jvegaf/mixduino/docs/midi/mixduino_dist.png

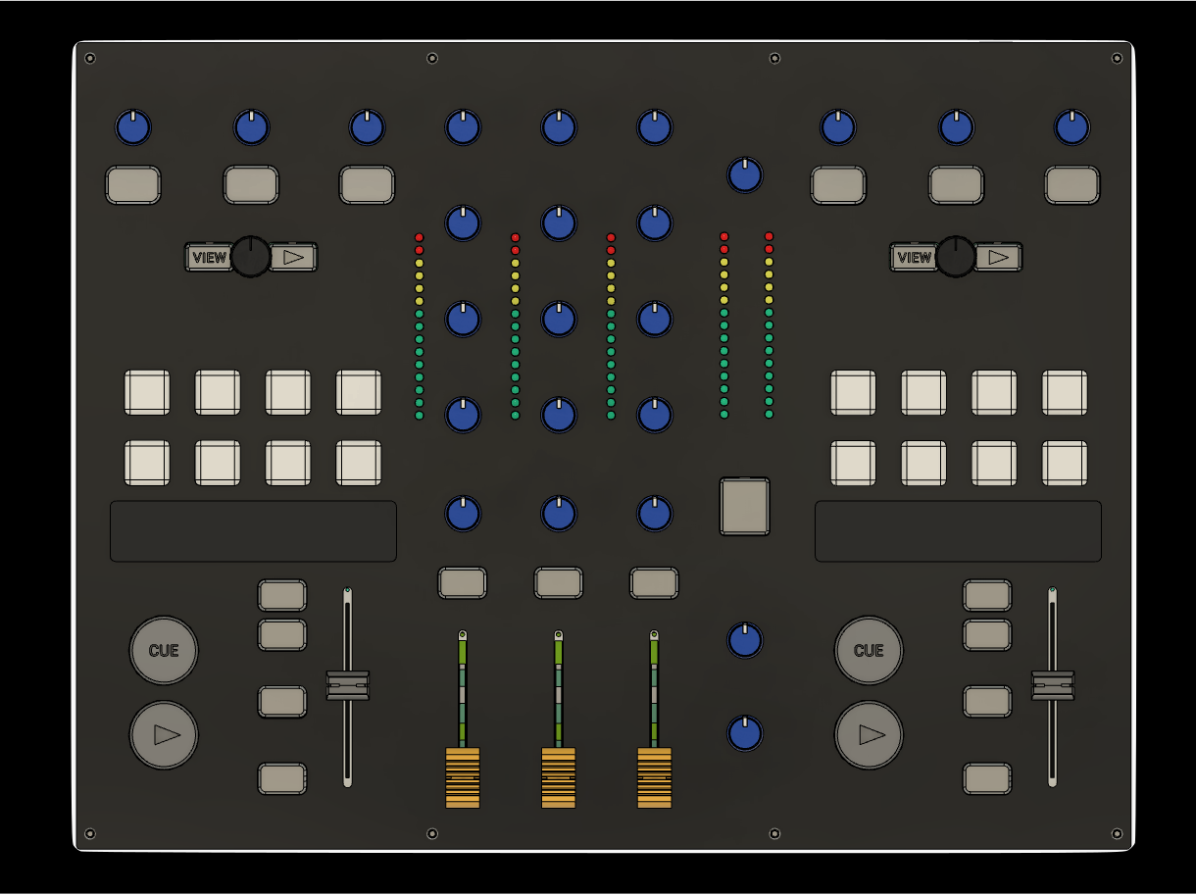
docs/midi/mixduino_dist.png
