jvegaf/mixduino/docs/pads/pads-dim1.png

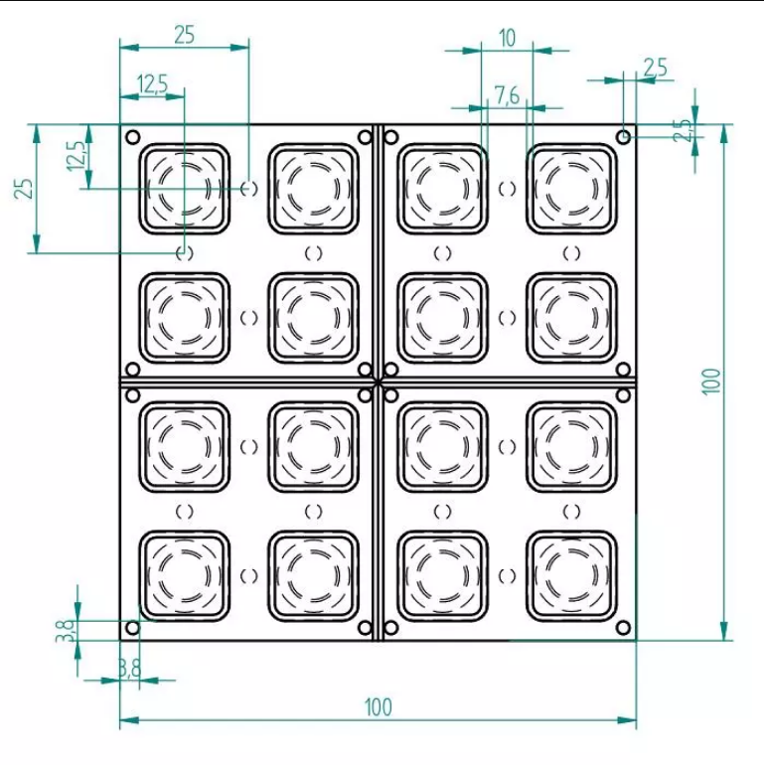
docs/pads/pads-dim1.png
