jvegaf/mixduino/docs/pads/pads-dim2.png

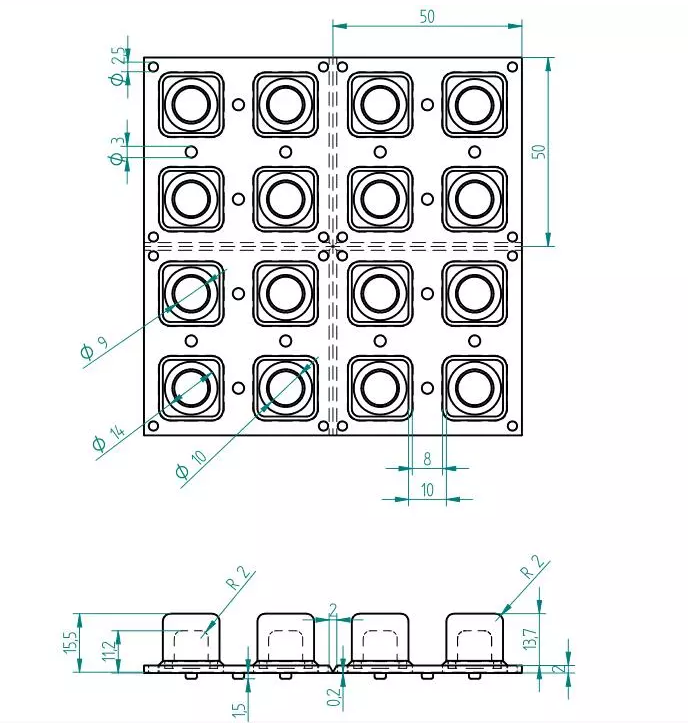
docs/pads/pads-dim2.png
