jvegaf/mixduino/PCB/Kicad/3d-models/WS2812B.step

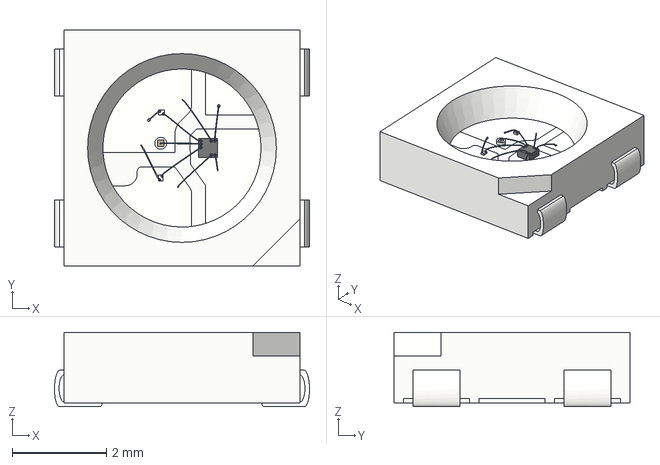
[picture p25: CAD file, 2021-04-04]
PCB/Kicad/3d-models/WS2812B.step
5.40 x 5.00 x 1.57 mm
