jvegaf/mixduino/PCB/Kicad/3d-models/Resistor_SMD_0,25W_1206.stp

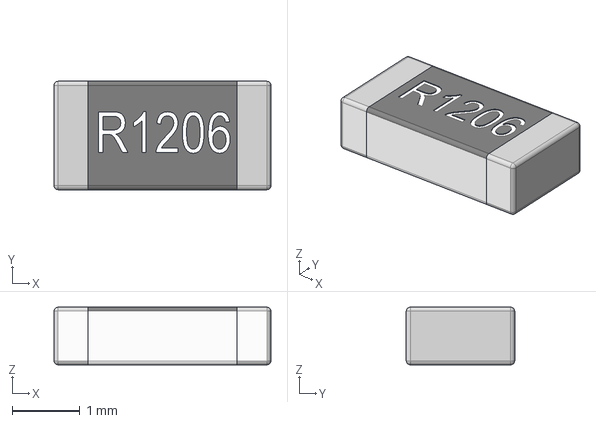
[picture p26: CAD file, 2021-04-04]
PCB/Kicad/3d-models/Resistor_SMD_0,25W_1206.stp
3.20 x 1.60 x 0.85 mm
