jvegaf/mixduino/PCB/Kicad/3d-models/LED D3 - Yellow_cutted.step

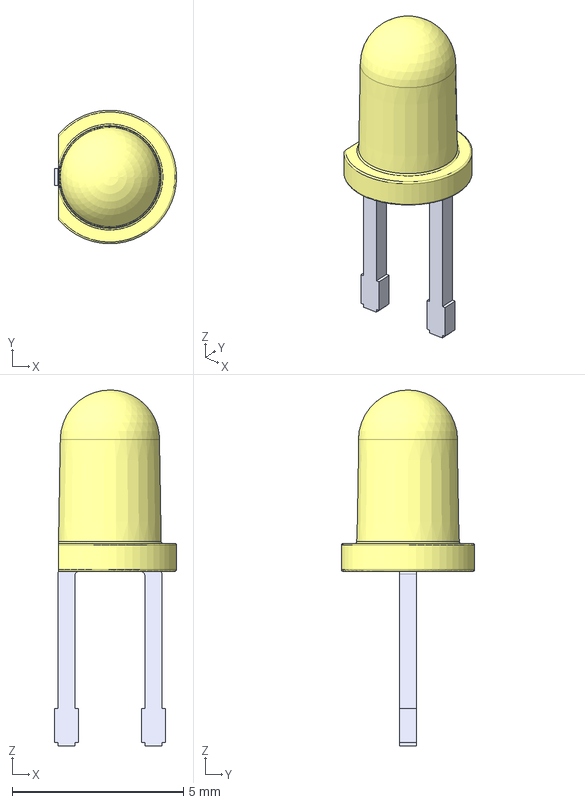
[picture p27: CAD file, 2021-04-04]
PCB/Kicad/3d-models/LED D3 - Yellow_cutted.step
3.57 x 3.90 x 10.4 mm
