jvegaf/mixduino/PCB/Kicad/3d-models/SW3dPS-SOIC24.STEP

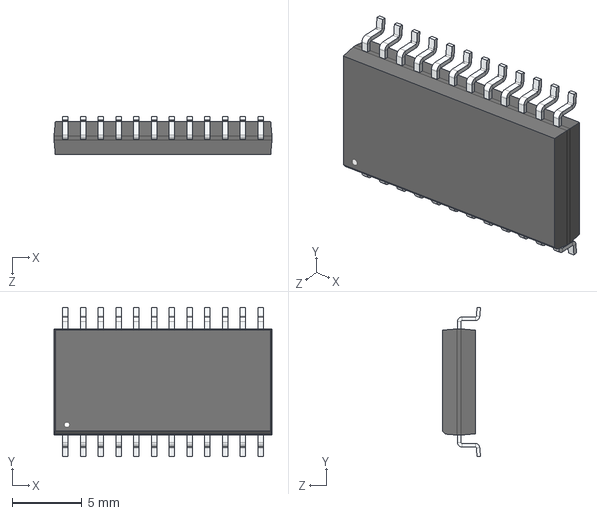
[picture p28: CAD file, 2021-04-04]
PCB/Kicad/3d-models/SW3dPS-SOIC24.STEP
15.6 x 10.7 x 2.72 mm
