jvegaf/mixduino/PCB/Kicad/3d-models/75mm Straight Slide Potentiometer.step

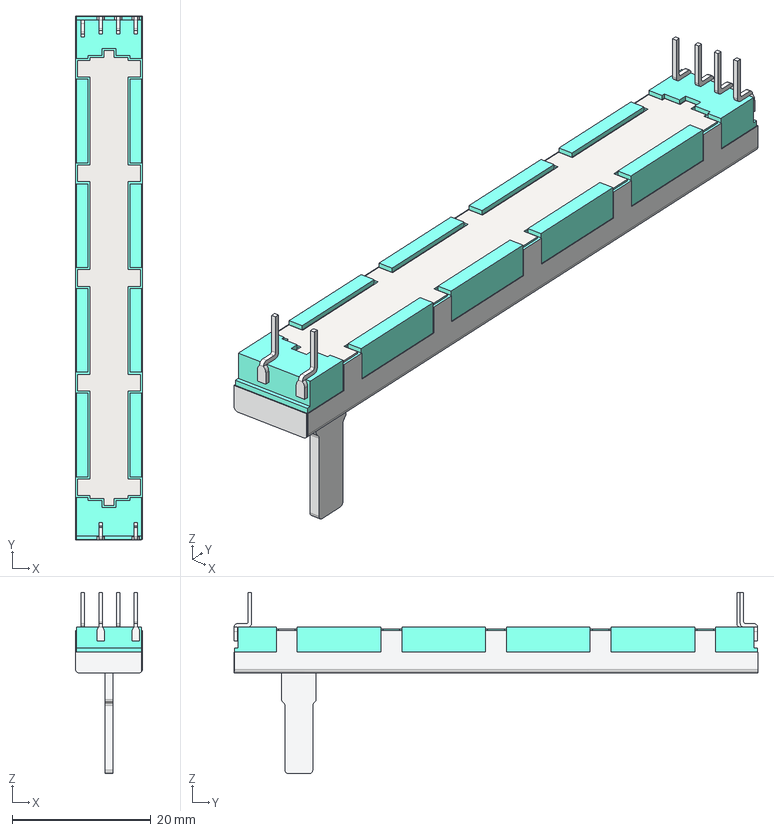
[picture p29: CAD file, 2021-04-02]
PCB/Kicad/3d-models/75mm Straight Slide Potentiometer.step
9.60 x 75.4 x 26.1 mm
Slide Por - Slider
Slide Pot - Pins x 6
