jvegaf/mixduino/PCB/Kicad/3d-models/EC11B-SW-Vert-20R-blue.step

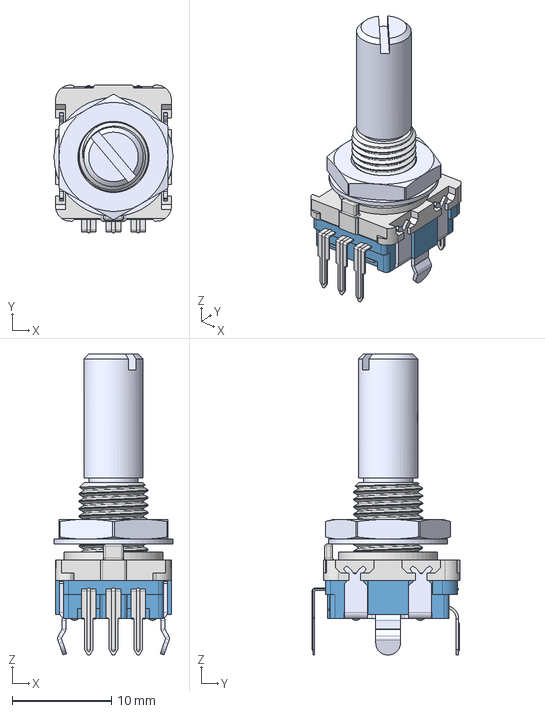
[picture p30: CAD file, 2021-04-02]
PCB/Kicad/3d-models/EC11B-SW-Vert-20R-blue.step
12.0 x 14.9 x 30.4 mm
