jvegaf/mixduino/PCB/Kicad/3d-models/SO-16.step

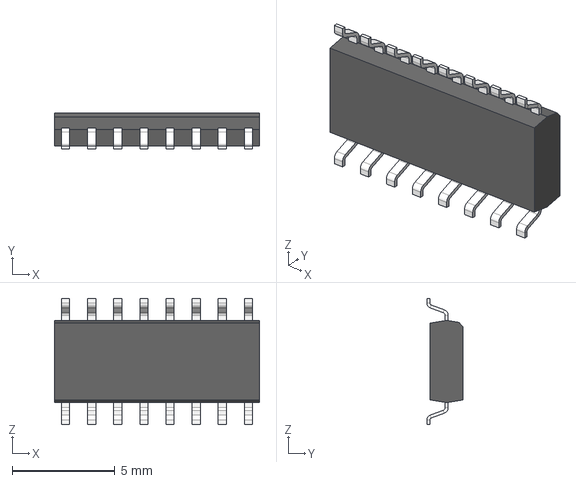
[picture p31: CAD file, 2021-04-02]
PCB/Kicad/3d-models/SO-16.step
9.97 x 1.76 x 6.14 mm
User_Library-so16-1
User_Library-so16-002
