jvegaf/mixduino/PCB/Kicad/3d-models/R-0904N-L-25KT-green.step

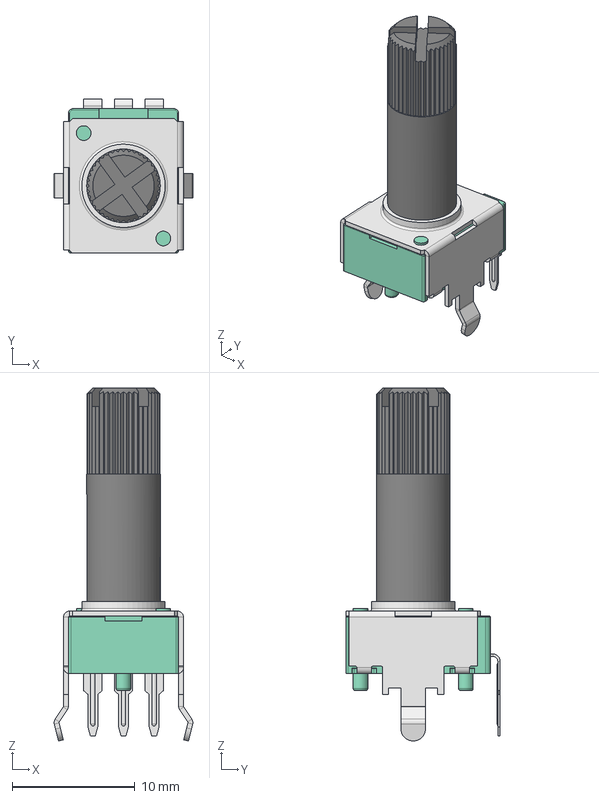
[picture p32: CAD file, 2021-04-02]
PCB/Kicad/3d-models/R-0904N-L-25KT-green.step
11.3 x 12.6 x 28.8 mm
