jvegaf/mixduino/Code/Mixduino/src/npMap.h

#ifndef ARDUINO_NPMAP_H
#define ARDUINO_NPMAP_H
#include <Arduino.h>

#pragma once


//////////////////////////////////////
// NEOPIXELS LEFT

uint8_t const NP_PADL_1        = 0;
uint8_t const NP_PADL_2        = 1;
uint8_t const NP_PADL_3        = 2;
uint8_t const NP_PADL_4        = 3;
uint8_t const NP_PADL_5        = 4;
uint8_t const NP_PADL_6        = 5;
uint8_t const NP_PADL_7        = 6;
uint8_t const NP_PADL_8        = 7;
uint8_t const NP_RANGE_L       = 8;
uint8_t const NP_SYNC_L        = 9;


//////////////////////////////////////
// NEOPIXELS RIGHT

uint8_t const NP_PADR_8       = 0;
uint8_t const NP_PADR_7       = 1;
uint8_t const NP_PADR_6       = 2;
uint8_t const NP_PADR_5       = 3;
uint8_t const NP_PADR_4       = 4;
uint8_t const NP_PADR_3       = 5;
uint8_t const NP_PADR_2       = 6;
uint8_t const NP_PADR_1       = 7;
uint8_t const NP_DECK_SEL     = 8;
uint8_t const NP_RANGE_R      = 9;
uint8_t const NP_SYNC_R       = 10;


#endif
